Neoanaloglab/Neobox/docs/glossary.zh-CN.md

# 术语表

[English](glossary.md) · **简体中文** · [日本語](glossary.ja.md)

> NeoBox 的文档里凡是默认你已经懂的词，这里都给一行定义，再给一行说明它在这个项目里为什么重要。其他页面会直接链到需要的那一条。

**目录：**[防牛顿环玻璃](#防牛顿环玻璃) · [基准 ISO](#基准-iso) · [打印床尺寸](#打印床尺寸) · [桥接](#桥接) · [相机翻拍](#相机翻拍) · [滑槽](#滑槽) · [翻拍台](#翻拍台) · [顶盖台](#顶盖台) · [扩散板](#扩散板) · [EFCS](#efcs) · [元件台阶](#元件台阶) · [象足](#象足) · [EV](#ev) · [片门](#片门) · [平场校正](#平场校正) · [闪光指数](#闪光指数) · [HSS](#hss) · [填充](#填充) · [混光腔](#混光腔) · [反相](#反相) · [承托](#承托) · [层高](#层高) · [定位榫与榫槽](#定位榫与榫槽) · [放大倍率](#放大倍率) · [手动出力档位](#手动出力档位) · [镜面对齐法](#镜面对齐法) · [牛顿环](#牛顿环) · [乳白](#乳白) · [敞开前口](#敞开前口) · [壁圈数](#壁圈数) · [压片窗插片](#压片窗插片) · [导轨](#导轨) · [raw](#raw) · [走片通道](#走片通道) · [片板](#片板) · [幻灯片板](#幻灯片板) · [支撑](#支撑) · [同步速度](#同步速度) · [TTL](#ttl) · [开窗](#开窗) · [工作距离](#工作距离)

## 词条 A–Z

这个项目同时用到胶片摄影和 3D 打印两个行当的词汇，很少有人两样都熟。下面每一条都是写给两样都不熟的人看的。词条按英文名的字母顺序排列。

> [!TIP]
> 零件名称是另一回事。每个零件只取一个名字，全篇不改。打印件：**主箱**、**顶盖台**、**胶片夹**（**夹底座** / **夹上盖**，每种画幅一对）、**压片窗插片**、**6×6 遮幅插片**、**幻灯片板**、**4×5 顶盖台**和**片板**。采购件：**扩散板**、**磁铁**、**钢垫片**，可选**防牛顿环玻璃**。原型机的**顶盖**和**胶片台**自 v1 起并入顶盖台；**抽口盖板**、**螺杆**和**螺母**已经取消：v1 全机没有任何紧固件。要是手里拿着一个件却对不上名字，去看[零件术语](printing.zh-CN.md#零件术语)，那里把每个名字都对应到一处你看得见的特征。

### 防牛顿环玻璃

一面经过细磨砂处理的玻璃，胶片压在上面也不会出[牛顿环](#牛顿环)。NeoBox 的可选压平升级件就是一片 64 × 95 × 2 mm 的单面 AN 玻璃，两种画幅通用。

**为什么重要：** 把它放进[元件台阶](#元件台阶)、替换掉打印的[压片窗插片](#压片窗插片)，它就给整格画面加上连续的封顶，把胶片任何位置的起伏都压在 0.28 mm 以内。磨砂面朝下，贴着胶片有光泽的片基面；药膜面朝着下方的开窗，什么都不接触。它的底面离焦平面只有 0.2 mm，落在上面的灰会进画面，装片之前先吹干净。

### 基准 ISO

基准 ISO（base ISO）是相机传感器的最低原生感光度，通常是 ISO 100，此时动态范围最大、噪点最少。

**为什么重要：** 箱内的闪光出力有富余，所以没有任何理由离开基准 ISO。测光从 ISO 100、f/5.6–f/8 起步。见[曝光](scanning.zh-CN.md#曝光)。

### 打印床尺寸

FDM 打印机打印床（build plate）的可打印面积，按 X × Y 标注。

**为什么重要：** 这是一票否决项，不是偏好问题。不过在 v1 里很容易过关。最大的零件是主箱和顶盖台，124.8 × 154.8 mm，所以 160 × 160 mm 的打印床就能打完全部零件；原型机时代关于 280 mm 大床的警告已经作废。见[你的打印机打得下吗](printing.zh-CN.md#你的打印机打得下吗)。

### 桥接

桥接（bridging）是把耗材直接横跨在两个已固定点之间的空隙上挤出，让它凌空成型，在下垂之前就冷却定形。

**为什么重要：** v1 里没有任何需要桥接的地方。主箱的前面不是一个被跨过的开口，而是干脆没有这面墙，也就是[敞开前口](#敞开前口)。十二个零件全部平面朝下、免[支撑](#支撑)打印。

### 相机翻拍

相机翻拍（camera scanning）是把底片架起来、用数码相机去拍，而不是送进平板扫描仪或滚筒扫描仪。也叫 DSLR scanning，不管你手里的是不是单反。

**为什么重要：** NeoBox 只做这件事的光源，别的都不做。它不夹相机，相机、镜头和支架都要你自己准备。见[什么是相机翻拍](getting-started.zh-CN.md#什么是相机翻拍)。

### 滑槽

胶片夹内部供片条横向滑动的槽，高 0.4 mm：135 胶片夹里宽 35.4 mm，120 胶片夹里宽 62.0 mm。槽底是[承托](#承托)，两侧是[导轨](#导轨)，槽顶是压片元件的底面，即搁在[元件台阶](#元件台阶)上的[压片窗插片](#压片窗插片)或[防牛顿环玻璃](#防牛顿环玻璃)。

**为什么重要：** 装片和过片都是捏着片头把胶片沿滑槽横向抽动完成的，中途既不开夹、也不动压片元件。拱起的一格在滑入时会被槽顶贴着压平。0.4 mm 这个数字，也是胶片夹零件值得用更细[层高](#层高)打印的原因。

### 翻拍台

翻拍台（copy stand）是底板上立一根立柱，把相机吊在可调高度上垂直向下拍。带横臂或可倒置中轴的三脚架干的是同一件活。

**为什么重要：** 胶片平面位于桌面以上 83.2 mm，支架要在这个高度之上再让出镜头的[工作距离](#工作距离)，同时还要把传感器保持在与胶片平行的姿态上。见[相机高度与支架](scanning.zh-CN.md#相机高度与支架)。

### 顶盖台

封住箱体顶部的那一个白色零件：原型机的顶盖和胶片台自 v1 起并成了这一件，124.8 × 154.8 × 10 mm。它的 6 mm 板搁在箱壁上，靠四个榫槽对准主箱的[定位榫](#定位榫与榫槽)；板上一圈凸缘围出 94.6 × 120.6 mm 的夹座，板身开有 62 × 95 mm 的透光窗、藏[扩散板](#扩散板)的暗槽，还嵌着四片与台面齐平的钢垫片，供胶片夹的磁铁吸附。可选的 4×5 版 `cover-stage-4x5.stl` 保留外形和榫槽，透光窗改为 102 × 126 mm，暗槽放 106 × 130 × 2 mm 的板，托盘 112.6 × 138.6 mm，给[片板](#片板)用。

**为什么重要：** 顶盖和胶片台合并之后，一整摞零件连同它们之间的公差都消失了：没有东西要调平，没有东西要拧。整件捏着凸缘就能提起，胶片夹在它上面磁吸掀换、几秒钟一换；凸缘顶比胶片平面低 0.2 mm，伸出夹外的胶片是搭在它上面走的，不会被顶住。

### 扩散板

一块半透明板材，把穿过它的光散成均匀的发光面。NeoBox 里只有一块：[乳白](#乳白)亚克力板，68 × 118 × 2 mm，装在[顶盖台](#顶盖台)内部透光窗下方的暗槽里。

**为什么重要：** 它本身就是那个发光面：光经过它之后，只剩 4.6 mm 空气就到胶片了。正因为它是漫射发光面，落在它上面的灰不会成像：定期擦拭即可，不必每次开工都伺候它。要取出来，掀掉胶片夹，从箱口伸手经透光窗把它向上顶出。

### EFCS

电子前帘快门（electronic first-curtain shutter）：曝光由传感器在电子端开始，由机械后帘结束。

**为什么重要：** EFCS 照样能触发闪光，而且省掉了前帘开启时的震动。*全*电子（静音）快门是另一个设置，通常根本触发不了闪光。见[曝光](scanning.zh-CN.md#曝光)。

### 元件台阶

夹底座外轨上那道 4.6 mm 高的台阶，承载压片元件（[压片窗插片](#压片窗插片)或[防牛顿环玻璃](#防牛顿环玻璃)），外侧再高出 0.4 mm 的一圈挡边防止元件走位。135 和 120 两种夹子的台阶完全相同，所以一片玻璃两边通用。

**为什么重要：** 它把压片元件的底面严格定在 4.6 mm，比胶片骑着的 4.2 mm [承托](#承托)高 0.4 mm，这个差值*就是*走片的[滑槽](#滑槽)。元件放上台阶装一次就不再动；过片是从它底下抽拉胶片完成的。

### 象足

象足（elephant foot）是打印件最初几层被喷嘴和热床压得略微外鼓的现象。

**为什么重要：** 它偏偏落在余量最小的配合上：[顶盖台](#顶盖台)底面那几个套住主箱[定位榫](#定位榫与榫槽)的榫槽口，还有压片窗插片坐进[元件台阶](#元件台阶)时的外轮廓。把切片软件里的象足补偿打开。见[打紧了或打松了怎么办](printing.zh-CN.md#打紧了或打松了怎么办)。

### EV

曝光值（exposure value）。1 EV 就是一档：到达传感器的光量翻倍或者减半。

**为什么重要：** 光的均匀度和曝光的一致性都用这个单位来评判：四角之间、一格与一格之间，而且总是在[平场校正](#平场校正)之后判读。

### 片门

界定一格画面曝光范围的那个矩形开口：在胶片相机里是机身上的金属片门，引申到这里，就是你透过去拍摄的胶片夹[开窗](#开窗)。

**为什么重要：** 不同机身的片门尺寸略有出入，所以胶片夹的开窗每边故意多做出约 0.5 mm，把这点差异和打印机的 XY 公差一并吃掉。它同时也是每次开工要吹干净的那个面；如果你用[防牛顿环玻璃](#防牛顿环玻璃)，就连它一起吹。

### 平场校正

平场校正（flat-field correction）是先单独拍一张均匀发光面，画面里不放胶片，再用实拍画面去除以这张参考片，让镜头暗角和光源本身的不均匀相互抵消。

**为什么重要：** 它排在最前面，先做完它，再来评判这只箱子。这是把镜头暗角和光源真实不均匀分开的唯一办法，箱子的均匀度要看的是校正之后剩下的那部分。见[平场校正与反相](scanning.zh-CN.md#平场校正与反相)。

### 闪光指数

闪光指数（GN，guide number）是闪光灯的出力标称值：闪光指数 = 光圈值 × 距离，对应 ISO 100 下的正确曝光。参考用的 NEEWER TT560 是 GN38，按米计。

**为什么重要：** 这是印在包装盒上的那个数字，而在 NeoBox 里它几乎什么都说明不了，因为闪光是从[敞开前口](#敞开前口)打进去的，光要经过若干次漫反射才能到胶片。测光从 ISO 100、f/5.6–f/8 起步，并做好把好几档出力交给箱体损耗的准备。

### HSS

高速同步（high-speed sync）：闪光灯发出一串快速的小脉冲，于是可以在高于相机[同步速度](#同步速度)的快门下使用。

**为什么重要：** 在这里毫无用处，而你很可能要为它多掏钱。在昏暗房间里靠闪光拍摄，你是主动选择在同步速度或更低的快门下工作的。

### 填充

填充（infill）是[壁圈数](#壁圈数)以内的网格结构，按占实心的百分比给出。

**为什么重要：** 十二个零件一律 15 %。v1 里再没有任何零件把负载压在填充上。让墙壁不透光的是壁圈数，不是填充。见[打印参数](printing.zh-CN.md#打印参数)。

### 混光腔

混光腔（integrating cavity）是一个内壁为哑光白的封闭空间，光在里面反复反射，直到方向和亮度都被彻底打匀。实验室里的对应物是积分球（integrating sphere）。

**为什么重要：** NeoBox 就是这样一个腔体：120 × 150 × 70 mm 的白色内腔，只有一面敞开。闪光灯平躺在桌面上、贴着[敞开前口](#敞开前口)向腔内水平打光，没有任何光对着胶片。均匀度来自白墙和白顶上的反复反射，不是仅靠扩散板。这也是内壁保持裸露白色耗材、绝不能上漆的原因。见[光是怎么走的](../README.zh-CN.md#光是怎么走的)。

### 反相

反相（inversion）就是把拍到的负片变成正像：反转影调、去掉彩色负片的橙色片基，再定下反差和色彩。

**为什么重要：** 这是整个流程的最后一步，也是恒定光源真正显出价值的地方：整卷每一张接受的闪光出力完全相同，所以一套反相配置通吃全卷。见[平场校正与反相](scanning.zh-CN.md#平场校正与反相)。

### 承托

夹底座内部供片边搁置的凸起座台，高出周围板面 0.4 mm，位于 4.2 mm 高度上。

**为什么重要：** 承托的上表面*就是*胶片平面。只有片条的边缘接触到它；影像区悬在开窗上方，头顶 0.4 mm 处是搁在[元件台阶](#元件台阶)上的压片元件。

### 层高

层高（layer height）是一层打印层的厚度。它把零件上每一个水平面的高度都量化了：凡是不等于层高整数倍的特征，都打不出设计尺寸。

**为什么重要：** 设计里所有高度都落在 0.2 mm 网格上，所有暴露台阶都不小于 0.4 mm。打印规格是所有件一律 0.2 mm 层高，每个高度都正好落在层边界上。见[打印参数](printing.zh-CN.md#打印参数)。

### 定位榫与榫槽

定位榫是凸起的小方块，榫槽是与之配合的凹口。主箱侧壁顶部立着四个 2.4 × 12 × 2.6 mm 的定位榫，插进[顶盖台](#顶盖台)底面的四个榫槽。

**为什么重要：** 这是全箱唯一的对位结构：v1 没有任何紧固件，整机靠重力堆叠，靠定位榫防止错位，每次都把透光窗对正在腔体上方。这也是组装态的箱子只能竖直提起、不能倾斜搬运的原因，也是[象足](#象足)补偿在榫槽口上格外要紧的原因。

### 放大倍率

放大倍率（magnification ratio）是被摄物在传感器上成像的大小除以它本身的大小。1:1（写作 1.0×）表示一格画面按原大投在传感器上。

**为什么重要：** 它决定你需要哪支镜头。全画幅拍满一格 135 需要 1.0×，拍满一格 6×6 需要 0.43×。任何一支 1:1 微距镜都能覆盖 NeoBox 支持的全部画幅，因为画幅越大，需要的放大倍率反而*越小*。见[放大倍率与镜头选择](scanning.zh-CN.md#放大倍率与镜头选择)。

### 手动出力档位

手动出力档位（manual power fraction）是用手把闪光出力设成满功率的一个分数：1/1、1/2、1/4，一路到 1/128，每一档正好差一整档。

**为什么重要：** 给这只箱子挑闪光灯只有两件事要紧，手动出力控制是其中之一。TT560 给出八个整档，档距偏粗，所以精细的曝光微调改用光圈的 1/3 档来做。

### 镜面对齐法

用眼睛把相机对正胶片的方法：在胶片位置平放一面小镜子，从取景器里看，移动相机，直到镜头自己的倒影正好居中。倒影居中，就说明传感器与胶片平面平行。

**为什么重要：** 它替掉了原型机的全部调平硬件：螺杆、螺母，一样不剩。在相机端对齐还顺带吸收了打印箱体的公差，因为你对正的是实际存在的那个胶片平面，而不是理应托着它的箱子。见[相机高度与支架](scanning.zh-CN.md#相机高度与支架)。

### 牛顿环

牛顿环（Newton rings）是胶片被压在玻璃或亚克力这类光滑表面上时出现的不规则彩色干涉条纹。

**为什么重要：** 这套设计没给它留任何生成的表面。用打印[插片](#压片窗插片)时，压根没有光滑表面接触影像区；用玻璃升级件时，贴着胶片的那一面特意做了磨砂，这就是[防牛顿环玻璃](#防牛顿环玻璃)里"防牛顿环"的含义；而药膜面朝着的是一个空开窗。

### 乳白

乳白（opal）是奶白色的半透明亚克力，光是在它的整个厚度里被散射的，而不是在一层磨砂表面上。

**为什么重要：** 乳白板和磨砂板不是同一种货：磨砂是透明板加一面哑光面，买错是很容易犯的错。NeoBox 需要一块 2 mm 乳白板，裁成 68 × 118 mm（原型机的 110 × 130 那块可以让店家裁小续用）。见[买对规格](bom.zh-CN.md#买对规格)。

### 敞开前口

主箱根本没有前墙：箱体前面整个敞开，闪光灯平躺在箱外桌面上、灯头怼着开口，向腔内水平打光。

**为什么重要：** 它让箱子跟任何一款具体的闪光灯脱了钩：什么品牌、什么尺寸都装得下，TT560 只是参考机。引闪接收器也留在箱外，信号干净，换电池不用开箱。环境光确实会进来：在昏暗房间里拍，别让顶灯直射箱口，闪光脉冲远远盖过剩下的那点环境光。

### 壁圈数

壁圈数（perimeters）指打印机在每一层边缘描出的那几圈实心轮廓，也叫壁或外壳。

**为什么重要：** 所有地方一律至少 3 圈。箱壁只有 2.4 mm 厚，而它的职责就是不透光；一堵大半是[填充](#填充)的墙会漏光。

### 压片窗插片

一块打印的框板，64 × 95 × 2 mm，中间开着片门式的窗：135 版 25 × 37 mm，120 版 57 × 85 mm。它搁在[元件台阶](#元件台阶)上，底面就是走片[滑槽](#滑槽)的槽顶。默认的压片元件。

**为什么重要：** 它在开窗四边给胶片做硬限位，把窗内起伏压在 0.28 mm 以内，1:1、f/8 时约 ±0.4 mm 的景深绰绰有余地盖住它。装一次就不再动；过片是从它底下抽拉片条完成的。压片元件里只有插片分幅面，[玻璃](#防牛顿环玻璃)则是一片通用。

### 导轨

夹底座上引导片条的凸起侧墙，高出[承托](#承托) 0.8 mm。内轨决定[滑槽](#滑槽)的宽度：135 胶片是 35.4 mm，两端各留 12 mm 的导向段；120 胶片是 62.0 mm。更靠外的外轨则托着[元件台阶](#元件台阶)。

**为什么重要：** 抽拉胶片时是内轨在扶着片条走；外轨从不接触胶片，它们的活是托住压片元件。装片之前，先用美工刀把槽口的毛刺修掉。

### raw

相机传感器未经处理的原始数据，在机内白平衡、反差曲线和 JPEG 转换之前就存了下来。

**为什么重要：** 一律拍 raw。[平场校正](#平场校正)和[反相](#反相)都作用在线性数据上，而 JPEG 已经把它们需要的余量扔掉了。

### 走片通道

胶片路径上必须保持净空的那条带，即中心线两侧各 31 mm 以内：在这个范围里，任何东西都不许升到接近胶片高度的位置，胶片夹两端之外也一样。

**为什么重要：** 比胶片夹 120 mm 更长的胶片，两头都要伸出去。夹内的净空由[导轨](#导轨)保证；夹外，[顶盖台](#顶盖台)的凸缘顶比胶片平面低 0.2 mm，片尾是搭在它上面走的：被托住，而不是被挡住。长片条建议用手托住远端。31 mm 是半宽；120 胶片的实际宽度约 62 mm。

### 片板

4×5 页片的一体式夹具 `sheet-plate-4x5.stl`：一块 112 × 138 × 5 mm 的板，上面一个 102.2 × 127.6 mm、深 2.0 mm 的片槽，槽底穿一个 97 × 121 mm 的开窗，再加两个边缺口。它立在 4×5 [顶盖台](#顶盖台)的托盘里，那块顶盖台代替标准顶盖台，并带着自己那块 106 × 130 × 2 mm 的乳白板。

**为什么重要：** 它就是 4×5 在原封不动的主箱上的全部路线：两个打印件加一次亚克力裁切。没有压片元件，因为 4×5 的放大倍率约 0.25×，f/8 下的景深大约 8 – 10 mm，页片的卷曲看不出来。它的混光余量只有 v1 的三分之一，所以 4×5 套件是作为实验发布的。

### 幻灯片板

装框 135 幻灯片的一体式夹具 `slide-plate-135.stl`：一块 94 × 120 × 5 mm 的板，上面一个 51.4 mm 见方、深 2.0 mm 的方槽，槽底穿一个 26 × 38 mm 的开窗，外加两个指槽。它代替 135 那副胶片夹立在[顶盖台](#顶盖台)的托盘里。

**为什么重要：** 幻灯片框比 0.4 mm 的[滑槽](#滑槽)厚许多倍，永远进不了胶片夹。这块板没有上盖、没有磁铁、没有压片元件：框是硬的，箱子是卧式的，方槽定位，重力压住。换上它就重新对焦；框里的胶片离片条的胶片面不到半毫米。

### 支撑

支撑（supports）是打在悬空结构下方的一次性脚手架，打完掰掉。

**为什么重要：** 十二个零件没有一个需要，全部免支撑打印：平面朝下，两个夹上盖则顶面朝下。硬开支撑只会在胶片滑过的表面上留下疤痕。见[十二个零件](printing.zh-CN.md#十二个零件)。

### 同步速度

同步速度（sync speed）是传感器在某一瞬间完全敞开的最快快门速度；只有在这个速度或更慢时，闪光才能照亮整幅画面，而不是其中一条带。

大多数现代无反和单反的同步速度是 **1/160 – 1/250 s**；不少老机型和中画幅是 1/125 s 或更慢；镜间快门则任何速度都能同步。你自己相机的数值写在说明书和规格表里，通常标作「X 同步」或「闪光同步」。

**为什么重要：** **设成 1/125 s，然后就别动了。** 这个值低于几乎所有相机的上限，还给廉价 2.4 GHz 无线引闪器的延迟留了余量。用引闪器时，**实际可用**的同步速度往往比标称值还要低一档。在这里放慢快门什么也不损失：在昏暗房间里拍摄，曝光实际上完全由那记脉冲决定。设错的症状是画面一部分正常曝光、另一部分是一条干净的暗带，因为闪光触发时快门帘还在扫过传感器。

不要指望相机自动帮你限制快门。很多机身只有在热靴上识别到闪光灯时才会限制，而无线发射器常常不会被识别成闪光灯。

### TTL

镜后测光闪光（through-the-lens）：相机先打一次预闪，测出结果，再自动设定闪光出力。

**为什么重要：** 在这里是用错了工具，而且不该为它花钱。你要的是每一张的出力*完全相同*，好让一套[反相](#反相)配置通吃全卷。这意味着手动出力，在校准时一次设定。

### 开窗

夹底座和夹上盖上供你透过去拍摄的那个洞：135 胶片夹 25 × 37 mm，120 胶片夹 57 × 85 mm。垫入 6×6 遮幅插片后，120 的画面收窄到 56.5 × 56.5 mm；幻灯片板的开窗是 26 × 38 mm，片板的是 97 × 121 mm。

**为什么重要：** 每个开窗相对名义画幅每边故意多做出约 0.5 mm，用来吸收不同相机之间的[片门](#片门)差异和打印公差。画面四周会露出一圈片边，后期裁掉。

### 工作距离

工作距离（working distance）是在给定[放大倍率](#放大倍率)下，镜头前端到被摄物之间的距离。放大倍率越高，它越短。

**为什么重要：** 它决定你的支架要多高。胶片平面位于桌面以上 83.2 mm，相机必须架在这个高度再加上你镜头工作距离之上，而且仍然要与胶片平行。见[相机高度与支架](scanning.zh-CN.md#相机高度与支架)。

---

← [故障排查](troubleshooting.zh-CN.md) · [文档索引](../README.zh-CN.md#文档) · [设计](design.zh-CN.md) →
