Neoanaloglab/Neobox/docs/scanning.zh-CN.md

# 翻拍扫描

[English](scanning.md) · **简体中文** · [日本語](scanning.ja.md)

> 这个项目的相机那一半：箱子上面要架什么、怎么把相机调到与胶片面平行、怎么对焦和曝光、怎么装片和过片，以及拿到 raw 文件之后该做什么。

**目录：**[开工之前](#开工之前) · [相机端器材](#相机端器材) · [放大倍率与镜头选择](#放大倍率与镜头选择) · [相机高度与支架](#相机高度与支架) · [平行度](#平行度) · [对焦](#对焦) · [曝光](#曝光) · [装片](#装片) · [装框幻灯片](#装框幻灯片) · [4×5 页片](#45-页片) · [拍完一卷](#拍完一卷) · [平场校正与反相](#平场校正与反相) · [出问题的时候](#出问题的时候)

## 开工之前

NeoBox 是[相机翻拍](glossary.zh-CN.md#相机翻拍)（camera scanning）用的光源：用数码相机去拍胶片，而不是把胶片送进扫描仪。这只箱子透过乳白亚克力把一个 62 × 95 mm 的透光窗照均匀，片条平整地保持在它上方 4.6 mm 处。从这里到一个数字文件之间的所有环节都在相机端完成，而相机端的东西，本项目一样都不提供。

架相机之前，先把这张单子走一遍：

- [ ] 主箱立在桌面上，顶盖台落在箱壁的定位榫上，乳白亚克力躺在它的暗槽里，**两面**的保护膜都已撕掉。
- [ ] 四片钢垫片平放在顶盖台的沉孔里，与台面齐平。
- [ ] 闪光灯平躺在桌面上，灯头怼在完全敞开的前口、朝腔内打光。任何热靴闪光灯都可以。T1 接收器跟着闪光灯留在箱外。
- [ ] 你要用的那副胶片夹已放进托盘凸缘围出的位置，压片元件（默认是压片窗插片，卷得厉害的胶卷换防牛顿环玻璃）已装在元件台阶里。
- [ ] 房间已调暗，没有任何顶灯直射敞开前口。
- [ ] 你已经用气吹把滑槽和压片元件吹过一遍；玻璃模式下，玻璃装进去之前两面都要吹。

> [!NOTE]
> 本设计还没有被打印出来，也没有被实际搭建过，所以下文没有任何一个数字是实测结果。曝光参数是用来起步和包围曝光的起点，不是预测值。

## 相机端器材

| 器材 | 在这里干什么 | 真正要紧的地方 |
|---|---|---|
| 机身 | 记录画面 | 手动曝光、raw 文件、能放大的实时取景、热靴，以及**机械快门**（或者开了之后仍然能触发闪光的 [EFCS](glossary.zh-CN.md#efcs)） |
| 具备微距能力的镜头 | 用一格画幅填满传感器 | 够不够你那个规格所需的放大倍率（见下表） |
| [翻拍台](glossary.zh-CN.md#翻拍台)（copy stand），或者带横臂、可倒置中轴的三脚架 | 把相机方方正正、稳稳当当地吊在透光窗正上方 | 先看刚性，再看立柱高度够不够 |
| 引闪发射器 | 触发箱外闪光灯上的接收器 | 必须能和你买的那个接收器配对；装在相机热靴上 |
| 快门线，或者自拍延时 | 让手离开相机 | 只要能不碰机身就把快门放掉，用什么都行 |
| 反相软件 | 把 raw 负片变成正像 | 见[平场校正与反相](#平场校正与反相) |
| 一面约 30 mm 的小平面镜 | 把传感器调到与胶片面平行 | 要平，而且小到能搁在胶片夹上 |
| 气吹 · 棉手套或洗净的双手 | 灰尘和指纹 | 和其他耗材列在一起 |

这些东西都不在制作成本里，闪光灯也不在。更完整的清单见[你需要自备的器材](getting-started.zh-CN.md#你需要自备的器材)；镜子、气吹和手套列在[工具与耗材](bom.zh-CN.md#工具与耗材)里。

发射器装在相机热靴上，接收器和闪光灯一起留在箱外的桌面上。两者必须设在同一频道，而且都要有电：频道没对上、接收器电池没电，都是画面全黑的常见原因。不过第一个该查的还是快门类型：见[曝光](#曝光)。

翻拍布置：NeoBox 立在桌面上，闪光灯平躺在敞开前口，相机架在翻拍台上、正对透光窗的上方，引闪发射器装在相机热靴上，接收器和闪光灯一起在箱外

## 放大倍率与镜头选择

[放大倍率](glossary.zh-CN.md#放大倍率)（magnification）指的是像在传感器上的尺寸除以被摄物本身的尺寸。1.0× 时，一格画幅按原大投到传感器上；0.5× 时，它在每个方向上只占一半。

把一格画幅拍满传感器所需的放大倍率（近似值，用来挑镜头）：

| 底片规格 | 画幅尺寸 | 全画幅（36 × 24） | APS-C（23.5 × 15.6） |
|---|---|---|---|
| 135 | 36 × 24 | 1.0×（一支 1:1 微距镜） | 0.65× |
| 6×4.5 | 56 × 41.5 | 0.58× | 0.38× |
| 6×6 | 56 × 56 | 0.43× | 0.28× |
| 6×7 | 56 × 70 | 0.34× | 0.22× |
| 6×9 | 56 × 84 | 0.29× | 0.19× |
| 4×5 | 96 × 120 | 0.25× | 0.16× |

任何一支 1:1 微距镜都覆盖表里的每一行；画幅越大，用到的放大倍率反而越低。最吃力的一档是全画幅拍 135，得用满 1.0×。

灰尘要按它落在哪个面上分，而不是按放大倍率分。落在乳白亚克力上的灰完全不会成像：扩散板本身就是发光面，落在上面的东西只是变成光的一部分，定期擦拭就行。会成像的，是落在胶片面上或者紧挨着胶片面的灰：胶片本身上的灰任何时候都成像；玻璃模式下，防牛顿环玻璃的底面离胶片面只有 0.2 mm，落在上面的灰会直接落进画面。这就是玻璃装进去之前要吹、[片门](glossary.zh-CN.md#片门)和滑槽每换一条片条都要吹的原因。光学上的推理见[设计](design.zh-CN.md#3-光学决策)。

## 相机高度与支架

胶片面位于**箱子落地面以上 83.2 mm** 的高度。这个高度由设计固定，135 和 120 完全一样：两副胶片夹把胶片托在同一个高度上，所以换规格不需要重新调平任何东西。例外都很小：6×6 遮幅插片把 120 胶片夹整体垫高 1 mm，装框幻灯片在约 82.6 – 83.6，4×5 页片在约 82.2。这是正常的，重新对个焦接着拍。到 4×5 变化很大的是工作距离：100 mm 微距在 0.25× 时前镜片要离胶片大约半米，先确认立柱够得着，或者换 50 – 60 mm 的微距，距离减半。

相机高度由两个数字推出来：

```
镜头前端到桌面 = 83.2 mm + 镜头在所需放大倍率下的工作距离
```

[工作距离](glossary.zh-CN.md#工作距离)（working distance）是镜头自身的属性，与箱子无关。先查出来或者量出来，再按下表检查支架：

| 买之前、定下来之前先确认 | 为什么 |
|---|---|
| 立柱行程从底板算起，能够到 83.2 mm 加上工作距离 | 微距镜做到 1:1 时要的高度，常常超出翻拍台的常规行程 |
| 松手之后云台不下坠 | 下坠反映到画面上，就是一卷拍下来焦点在慢慢跑 |
| 底板明显大于箱子 124.8 × 154.8 mm 的占地，箱子前方还要留出放闪光灯的桌面 | 箱子要放正，闪光灯要平躺在敞开前口，你的手还得有地方伸 |
| 镜头光轴能落到透光窗中心，而立柱不会顶到箱子 | 倒置中轴的三脚架，常常把一条腿正好支在箱子该待的位置上 |

高度定好之后要记录下来，方便随时回到同一状态：在桌面或者垫子上标出箱子的占位（两根定位销，或者干脆贴胶带），再把每个规格对应的立柱高度写下来。换规格只改放大倍率，胶片面不动。要挪箱子就水平地整体端起来：装好的这一摞靠重力和磁铁保持在一起，没有任何紧固件。

## 平行度

> [!IMPORTANT]
> 先保平行度，再谈均匀性。闪光脉冲能冻住震动，但箱子里没有任何东西能救回一个与传感器不平行的胶片面：那样每一格都会有一条边是虚的。

用镜子，别用眼睛：

1. 把那面小平面镜放在胶片面上，也就是搁在胶片夹上。
   *检查点：*镜子平放，不晃。
2. 用实时取景透过相机看这面镜子。
   *检查点：*你能看到镜头和相机正面被反射回来。
3. 移动相机，直到这个反射正好落在画面中心，而且看上去左右对称。
   *检查点：*反射出来的镜筒是同心的，不是被挤到一边的椭圆。镜头的反射落在正中的时候，传感器就与胶片面平行了。
4. 在相机端修正，不要动箱子：调翻拍台云台的倾角（云台没有倾角调节就在座下垫薄片），然后重新检查。两轮就能收敛。箱体上没有任何调平机构；镜面对齐法顺带把箱体的打印公差一起吸收掉。
   *检查点：*手从所有东西上拿开之后，反射仍然居中。

<details>
<summary>镜子为什么管用，而水平仪为什么不管用</summary>

水平仪参照的是重力。而你真正需要的是传感器平面与胶片面平行：相机可以完全水平，却仍然相对箱子是歪的；箱子也可以是水平的，而相机吊在一条正在下坠的横臂上。

镜子把重力从这道题里拿掉了。只有当镜面垂直于光轴时，镜子才会把镜头沿着光轴原样反射回来。反射居中且左右对称就意味着垂直，垂直于光轴就意味着平行于传感器。这是一个零位法，越接近正确它越灵敏。
</details>

箱子或者相机被动过之后，就重新校一次平行度。[每次开工](assembly.zh-CN.md#换幅面与日常操作)里的流程，默认平行度已经是对的。

## 对焦

1. 给房间留一点刚够看清胶片细节的光，但别让任何灯直射敞开前口。
   *检查点：*你能在开窗里看清胶片细节。
2. 装上片条，把第一格抽拉到开窗里。
   *检查点：*画幅在开窗里居中，没有片边线侵进来。
3. 进实时取景，放大到 100 %。
   *检查点：*放大后的画面是稳的，显示的是画幅上的一小块，不是一整格。
4. 对着**颗粒**对焦，不要对着画面内容对。颗粒长在胶片面上，画面里那些本来就边缘柔和的被摄物不在。
   *检查点：*你能分辨出一颗颗的颗粒团，而不只是「画面变清楚了」。
5. 收到你实际要拍的那档光圈，重新检查中心和两个对角。
   *检查点：*中心和两个角上的颗粒都是脆的。如果有一个角怎么都实不了，回到[平行度](#平行度)。
6. 把镜头切到手动对焦，或者拿胶带把对焦环粘住，这一场剩下的时间都不要再碰它。
   *检查点：*拨对焦环没有反应，或者胶带把它固定住了。

## 曝光

| 项目 | 设置 | 为什么 |
|---|---|---|
| 模式 | 手动 | 这里没有任何东西该逐格变化 |
| ISO | [基准 ISO](glossary.zh-CN.md#基准-iso)（base ISO），通常是 100 | 闪光出力有富余，那就选画质最干净的那一档 |
| 光圈 | 从 f/5.6–f/8 起步 | 这只箱子的测光起点 |
| 快门 | **1/125 s**，等于或低于相机的[同步速度](glossary.zh-CN.md#同步速度)（sync speed） | 快过同步速度，快门帘会在画面上切出阴影：焦平面快门的极限在 1/160–1/250，廉价 2.4G 引闪还要再吃掉大约一档。1/125 s 低于几乎所有相机的上限，还留有余量 |
| 快门类型 | 机械快门；如果你的相机开了 EFCS 仍然能触发闪光，EFCS 也行 | 见下面的警告 |
| 文件 | [raw](glossary.zh-CN.md#raw) | 反相需要线性数据 |
| 白平衡 | 固定，取什么值都行 | 后期用片基来定 |
| 防抖 | 关 | 架在支架上时它会自己来回找补，反而把画面弄虚 |
| 闪光灯 | 手动出力 | [TTL](glossary.zh-CN.md#ttl) 和 [HSS](glossary.zh-CN.md#hss) 在这里没有任何用处 |

> [!WARNING]
> 全电子快门通常根本不会触发闪光。如果第一张全黑，先去菜单里查快门类型，再查别的。

找到工作出力：

1. 把闪光出力设到 1/8 起步。任何能手动出力的热靴闪光灯都行；参考机型 TT560 的[手动出力档位](glossary.zh-CN.md#手动出力档位)（manual power fraction）从 1/1 到 1/128 按整档分：一共八档，中间没有别的。
   *检查点：*闪光灯的充电完成指示灯亮起。
2. 胶片夹里放着片条，拍一张试拍。
   *检查点：*画面不是全黑：闪光灯响了，引闪也配对上了。
3. 看直方图。格与格之间那段透明片基是画面里最亮的东西；曝光到它刚好不溢出为止。
   *检查点：*你能在直方图右端找到片基那个峰，并看清它离右边缘还有多远。
4. 粗调用闪光出力，细调用光圈的 1/3 档。闪光灯只能整档跳，细活由光圈来做。
   *检查点：*透明片基落在直方图右边缘略靠里的位置，没有溢出警告。
5. 锁定，整卷都不再改。
   *检查点：*闪光出力和光圈都写了下来。

相对于裸光源的读数，要预计为箱内的反弹光路多付出几档闪光出力。本设计还没有被搭建出来，没有任何损耗数字，所以把 1/8 只当作起点，靠包围曝光去找。

> [!TIP]
> 闪光灯和 T1 接收器都在箱前的桌面上：改出力不用碰箱子，给接收器换电池也不用打开任何东西。出力在校准时一次定好，之后细活交给光圈。两套镍氢电池轮换用。

<details>
<summary>为什么说闪光脉冲就是曝光，以及它为什么让你能在基准 ISO 下拍</summary>

箱子的前口是敞开的，但在昏暗的房间里这不改变任何事情：闪光脉冲比房间从开口漏进去的那点光亮出几个数量级。快门在近乎黑暗中打开，闪光灯放光，快门关闭，所以**闪光脉冲就是曝光**，它在工作出力下的持续时间是 1/1,000 到 1/20,000 s。

这相当于一个有效快门，比连续发光的 LED 灯板在 ISO 100、f/8 下所需的 1/15 到 1/60 s 真实快门时间短一到三个数量级。振动、快门震动和地面传来的低频晃动都不再是问题。

干活的时候你还会感受到另外两个后果：

- 每一格得到的输出完全一样，所以一套反相参数通常够用一整卷。
- 氙气管给出的是真正连续、接近日光的光谱，约 5600 K，彩色负片在这种光下比在窄带光源下好伺候得多。
</details>

## 装片

> [!CAUTION]
> 每装一条片条之前，都要把两个滑槽口和压片元件吹一遍；玻璃模式下，玻璃装进去之前两面都要吹。胶片在一条 0.4 mm 的空间里滑行；卡在里面的一粒砂，会把你之后抽拉过去的每一格都划伤，而划伤的底片是修不回来的。

| 胶片夹特征（mm） | 135 | 120 |
|---|---|---|
| 滑槽宽度 | 35.4 | 62.0 |
| 滑槽高度 | 0.4 | 0.4 |
| 开窗 | 25 × 37 | 57 × 85（整格 6×9） |
| 外形，两件相同 | 94 × 120 | 94 × 120 |

两种压平模式共用同一副胶片夹，胶片操作在两种模式下完全一样：

- **压片窗插片（默认）。** 一片打印的 64 × 95 × 2 框，每个幅面各一片，在开窗四边对胶片做硬限位。残余起伏不超过约 0.28 mm，落在 1:1、f/8 下约 ±0.4 mm 的景深之内。
- **防牛顿环玻璃（卷片严重时的升级件）。** 一片 64 × 95 × 2 的 AN 玻璃两个幅面通用，对整个画幅连续封顶，任何位置都压在同样的 0.28 mm 之内。磨砂的 AN 面朝**下**，贴着光亮的片基面，这对组合不起[牛顿环](glossary.zh-CN.md#牛顿环)（Newton rings）；药膜面朝着下方的开窗，什么都不碰。

装元件，一种模式装一次，不用每条片条都动：

1. 吹压片元件，玻璃模式下尤其要吹底面：它离胶片面只有 0.2 mm，落在上面的灰会直接落进画面。然后把元件放进夹底座的 4.6 mm 元件台阶里。
   *检查点：*元件平躺在台阶里，不晃。
2. 盖上夹上盖。闭合磁铁把三明治吸紧，上盖的限位腔把元件圈住，只留一点浮动余量。
   *检查点：*夹上盖平整落位。
3. 把胶片夹放进顶盖台的托盘凸缘里；底座里的磁铁吸在嵌入台面的钢垫片上。
   *检查点：*胶片夹在凸缘里落稳，不晃。

然后每条片条：

1. 从两个滑槽口把滑槽吹一遍。
   *检查点：*对着光看，滑槽里没有肉眼可见的灰。
2. 从任意一个滑槽口进片，轻轻推到片头从另一侧伸出来。默认**哑光的乳剂面朝下**、光亮的片基面朝上；导向轨会把片条引到元件下面，胶片夹全程不打开。
   *检查点：*只用手指的力就能推动片条。绝对不要硬塞。
3. 注意拱向。卷得明显的片条，插片模式拱面朝**下**装，玻璃模式拱面朝**上**装。如果这样一来乳剂面朝上了，实时取景里边缘字码会读成镜像；后期把画面翻回来就行，别跟胶片较劲。
   *检查点：*片条平躺在滑槽里，槽口处没有翘起来。
4. 捏住伸出夹外的片头，抽拉到第一格在开窗里居中。
   *检查点：*画幅居中，没有片边线侵进来。

取放要点：

- **片条也行，整卷也行。** 超出胶片夹的部分从两端敞开的槽口伸出去，搭在托盘凸缘上；凸缘特意做得比胶片面低 0.2 mm，就是为了当这个支托。片条很长时，用另一只手托住远端，别让它在凸缘的棱上拖擦。
- **过片靠捏住片头抽拉。** 一卷拍完之前不打开胶片夹：捏住伸出来的那头直接抽，插片模式和玻璃模式动作完全一样。拱起的部位滑过时会被元件底面压平。
- **换幅面 = 换夹子。** 把整副胶片夹克服磁力掀起来，换上另一副，几秒钟的事，什么都不用重新调平。
- **拿片捏边**，手洗干净，或者戴棉手套。
- **6×6** 用 120 胶片夹，把 `mask-6x6.stl` 垫在底座**下方**、托盘里；胶片夹整体抬高 1 mm，正常现象，重新对个焦。**6×4.5** 没有专用遮幅：在 120 开窗里拍，后期裁切。
- **装框幻灯片**放进幻灯片板，从不放进胶片夹：见[装框幻灯片](#装框幻灯片)。

<details>
<summary>为什么胶片出来是平的，以及为什么一定要在后期裁切</summary>

胶片的边缘骑在夹底座的承台上，比压片元件的底面低 0.4 mm，形成一条四边加全幅宽度都有硬限位的通道。用插片时，影像区完全没有任何东西接触，起伏最多约 0.28 mm，1:1、f/8 下约 ±0.4 mm 的景深足以覆盖。用 AN 玻璃时，整个画幅被连续封顶，任何位置都压在同样的 0.28 mm 之内，而药膜面依然什么都不碰：玻璃的磨砂面贴着光亮的片基面，这对组合不起[牛顿环](glossary.zh-CN.md#牛顿环)（Newton rings），而药膜面朝着下方的开窗。

开窗相对标称画幅每边**刻意放大 0.5 mm 左右**（135 标称 24 × 36，120 标称 56 × 84）。这是为了吸收不同机身之间的片门差异，以及不同胶片夹之间的打印机 XY 公差。代价是画幅四周会露出一条片边，后期裁掉。完整几何见[设计](design.zh-CN.md#5-胶片夹)。
</details>

## 装框幻灯片

幻灯片框厚约 1.2 – 3.2 mm，滑槽只有 0.4，所以装框的幻灯片永远进不了胶片夹。它有自己的零件 `slide-plate-135.stl`：一块代替 135 胶片夹立在托盘里的板，上面一个 51.4 mm 见方的方槽，槽下一个 26 × 38 mm 的开窗。没有上盖、没有磁铁、没有压片元件：框是硬的，箱子是卧式的，方槽定位，重力压住。

1. 把 135 胶片夹从托盘里掀出来，放进幻灯片板。
   *检查点：*板子平躺在凸缘里，不晃。
2. 吹净方槽和幻灯片的两面。
3. 把框放进方槽，放法和你拿着它对着窗看时一样：从上往下看图像是正的，这样药膜就朝下。
   *检查点：*框坐在槽底上，开窗被完全盖住。
4. 重新对焦。框里的胶片在约 82.6 – 83.6 mm 处，不是片条的 83.2，纸框和塑料框还各不相同；每换一种框，对着颗粒对一次焦。
5. 从方槽两侧的指槽把框抠出来，换下一张。

翘曲的纸框，或者在放映机里鼓起来过的片子，这里没有任何东西能压平，专用的幻灯片扫描仪也一样；1:1、f/8 下约 ±0.4 mm 的景深能吃掉大部分。玻璃框原样放进去。开窗比任何框的片窗都大，所以框住画面的是框自己：后期按它裁切。

## 4×5 页片

4×5 要用可选的 4×5 套件：`cover-stage-4x5.stl` 代替顶盖台，它的暗槽里放自己那块 106 × 130 × 2 的乳白板，`sheet-plate-4x5.stl` 立在它的托盘里，用 102.2 × 127.6 的片槽接住 101.6 × 127 的页片，槽下开 97 × 121 的窗。主箱、闪光灯和支架都不变。

1. 抓着凸缘把顶盖台掀下来，把 4×5 顶盖台放到同一组四个定位榫上，它的亚克力已经在暗槽里。
   *检查点：*它靠自重落到定位榫上，和顶盖台完全一样。
2. 把片板放进托盘。
   *检查点：*板子平躺在凸缘里，不晃。
3. 吹净片槽和页片的两面，把页片放进去，放法和你拿着它对着窗看时一样：从上往下看图像是正的，药膜朝下。
   *检查点：*页片平躺在槽底上，开窗被完全盖住。
4. 重新对焦并重设立柱：全画幅拍 4×5 约为 0.25×，页片在约 82.2 mm 处。0.25×、f/8 下的景深大约 8 – 10 mm，所以卷曲的页片不是对焦问题。
5. 从两个边缺口把页片抠出来。

**唯一的未知数是均匀性。** 4×5 的窗口离混光腔壁只有 9 和 12 mm，而 v1 是 29 和 27.5。先拍一张空白片看一看：如果出现你不能接受的渐变，[平场校正](#平场校正与反相)能在后期把它去掉，[设计 §10](design.zh-CN.md#10-45-装在-v1-主箱上)则写了能把余量补回来的大箱子。

## 拍完一卷

```mermaid
flowchart TD
    A[吹滑槽和压片元件] --> B[进片，片头穿出另一侧]
    B --> C[抽拉到第一格进开窗]
    C --> D[对着颗粒对焦一次]
    D --> E[试拍一张：看直方图]
    E --> F{片基刚好不溢出？}
    F -- 否 --> G[用光圈调 1/3 档]
    G --> E
    F -- 是 --> H[拍这一格，raw]
    H --> I[捏片头抽拉过片]
    I -->|还有格| H
    I -->|这条拍完| J[拍一张平场帧]
```

每一格要做的全部事情是：捏住片头抽拉到下一格在开窗里居中，手离开，用快门线放掉快门，重复。

*每格的检查点：*按快门之前，开窗里没有画幅边缘或者片边线侵进来。

第一卷就值得养成的习惯：

- **给这一卷打个板。** 第一张影像之前，先拍一张写着卷号的卡片。文件不用改名就自动按卷分组了。
- **收工时也拍一张平场帧**，不只是开工时拍，这样你才知道中途有没有东西动过。
- **一卷之中不要改闪光出力。** 闪光灯就摊在桌面上，伸手就能碰到；忍住，改一次出力就毁掉「一卷一套反相参数」这个便利。
- **每换一条片条都吹一遍。**

每小时能拍多少，取决于你定下的那个出力对应的闪光灯回电时间，以及你逐格检查得有多仔细。本设计没有任何张数／小时的数据，因为它还没有被搭建出来。长时间连续拍摄，实际做法是两套镍氢电池轮换。

## 平场校正与反相

按顺序来。先[平场校正](glossary.zh-CN.md#平场校正)（flat-field correction），后[反相](glossary.zh-CN.md#反相)（inversion）：正像上的平场很难判断，而给没做过平场的画面反相，等于把暗角一并固化进片子里。

**拍平场帧。** 胶片夹里不放胶片，其余一概不动（同一光圈、同一焦点、同一高度），拍一张裸露发光面的 raw。这一张同时记录了镜头暗角和光源本身的不均匀。

**套用它。** 把每一格除以这张平场帧，就能把两者一次去掉。剩下的，就是光源自己的表现。

**验一下。** 在校正后的平场帧上，四个角各取一小块、中心取一块，互相比较。一条实用的验收带是四角之间约 ±0.1 [EV](glossary.zh-CN.md#ev)，而且是做完平场校正之后衡量的。这条带首尾合计 0.2 EV，线性比值 2^0.2 ≈ 1.15，所以你要找的是：线性 raw 数值里，最亮和最暗的采样之间相差不到大约 15 %。如果没达到，办法在光源那头（闪光灯怎么怼在敞开前口上），不在相机上。

能干这两件事的软件，列出来只是因为它们确实存在、也确实常用，不构成推荐：

| 工具 | 平场校正 | 反相 |
|---|---|---|
| RawTherapee | Raw 选项卡里的 Flat-Field 工具 | Film Negative 工具 |
| ART | 与 RawTherapee 同源 | 支持负片反相 |
| darktable | — | `negadoctor` 模块 |
| Capture One | LCC（lens cast calibration） | — |
| Lightroom + Negative Lab Pro | 通过插件或者一个相除图层 | Negative Lab Pro |

然后反相：

1. **用透明片基定白平衡。** 取格与格之间未曝光的那段片边：彩色负片上那就是橙色片基，把它中性化，反相才会听话。
   *检查点：*片边读起来接近中性灰，不再发橙。
2. **反相**，用你选定的那个工具。
   *检查点：*画面读起来是正像，整体没有残留的色偏。
3. **把参数复制到整卷。** 因为每一格接受的闪光输出都相同，一套反相参数通常够用一整卷。定稿之前抽查一格厚的和一格薄的。
   *检查点：*厚的那格和薄的那格反相之后都不溢出。
4. **裁到画幅。** 开窗是故意做大的，把那条片边裁掉。
   *检查点：*四边都不留片边，也不留胶片夹的边缘。

**黑白胶片**没有橙色片基，但取片基采样一样能给出一个可用的中性参考。

## 出问题的时候

| 现象 | 先查这里 |
|---|---|
| 整张全黑 | 快门类型（电子快门不会触发闪光）、同步速度、接收器电池、引闪频道 |
| 画面上出现一条干净的暗带 | 快门快过了有效同步速度：焦平面快门的极限在 1/160–1/250，廉价 2.4G 引闪还要再吃掉大约一档。降回 1/125 s |
| 只有一条边发虚 | [平行度](#平行度)，不是对焦 |
| 逐格位置都不变的柔边光斑 | 胶片面上的灰：在胶片上，或者玻璃模式下在玻璃底面。吹干净重拍平场帧；扩散板本身的灰不成像 |
| 一卷拍下来曝光在漂 | 闪光出力被碰过（闪光灯就摊在桌面上），或者电池快没电了 |
| 做完平场校正四角仍然不均 | 问题在光源不在镜头：把灯头重新怼正在敞开前口上，重拍平场帧 |

完整的现象—原因—处理表，包括那些以拍摄问题的形式暴露出来的打印和装配缺陷，在[故障排查](troubleshooting.zh-CN.md#拍摄)里。

---

← [装配](assembly.zh-CN.md) · [文档索引](../README.zh-CN.md#文档) · [故障排查](troubleshooting.zh-CN.md) →
